Taxom/RO_controller/photos/photo_2024-03-21_01-51-23.jpg

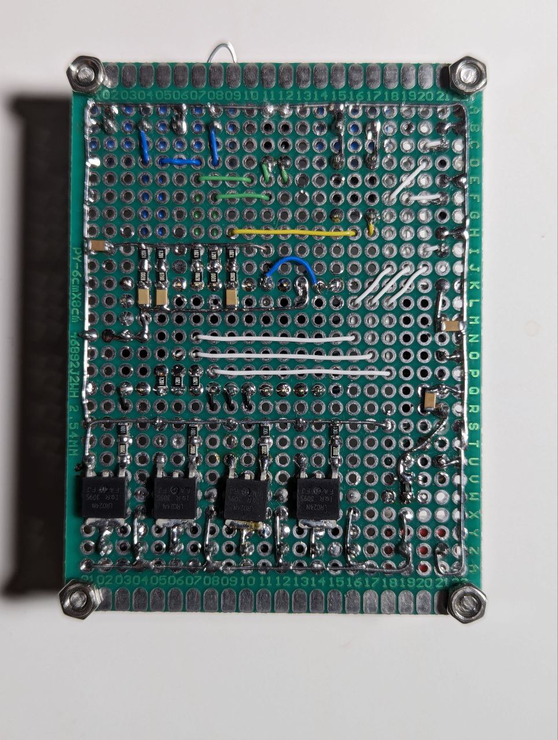
photos/photo_2024-03-21_01-51-23.jpg
